forgevolt/VectorArcade/mechanics/print-profiles/TintinRocketShooter/TinTinRocket-Top-H2D-PLA-GF Support.3mf

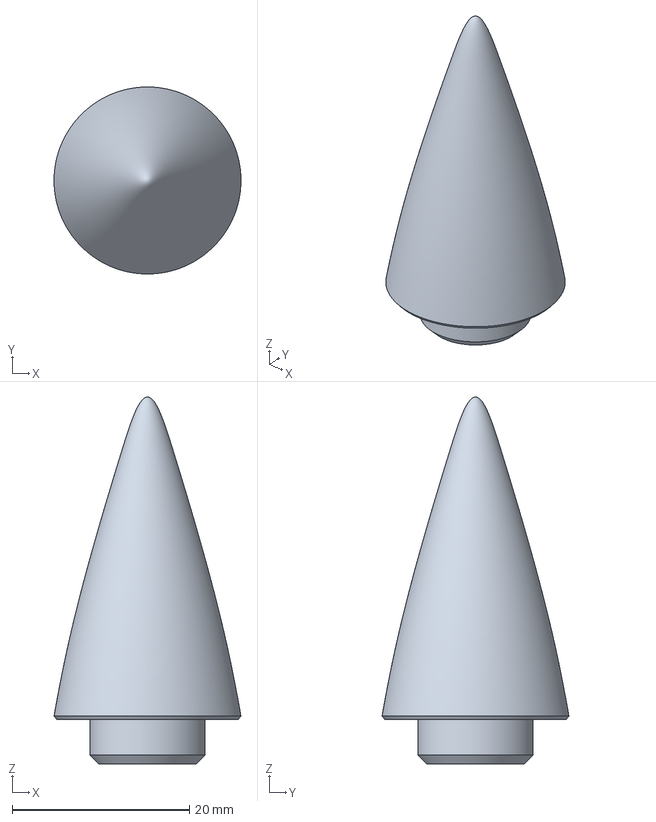
[picture p17: CAD file, 2026-09-30]
mechanics/print-profiles/TintinRocketShooter/TinTinRocket-Top-H2D-PLA-GF Support.3mf
21.1 x 21.1 x 41.4 mm
